o7-machinehum/flipper-blackhat-a33/electronics/nff_pcb/a33_power.kicad_sch

## KiCad design electronics/nff_pcb/a33_power.kicad_sch (2024-08-12)

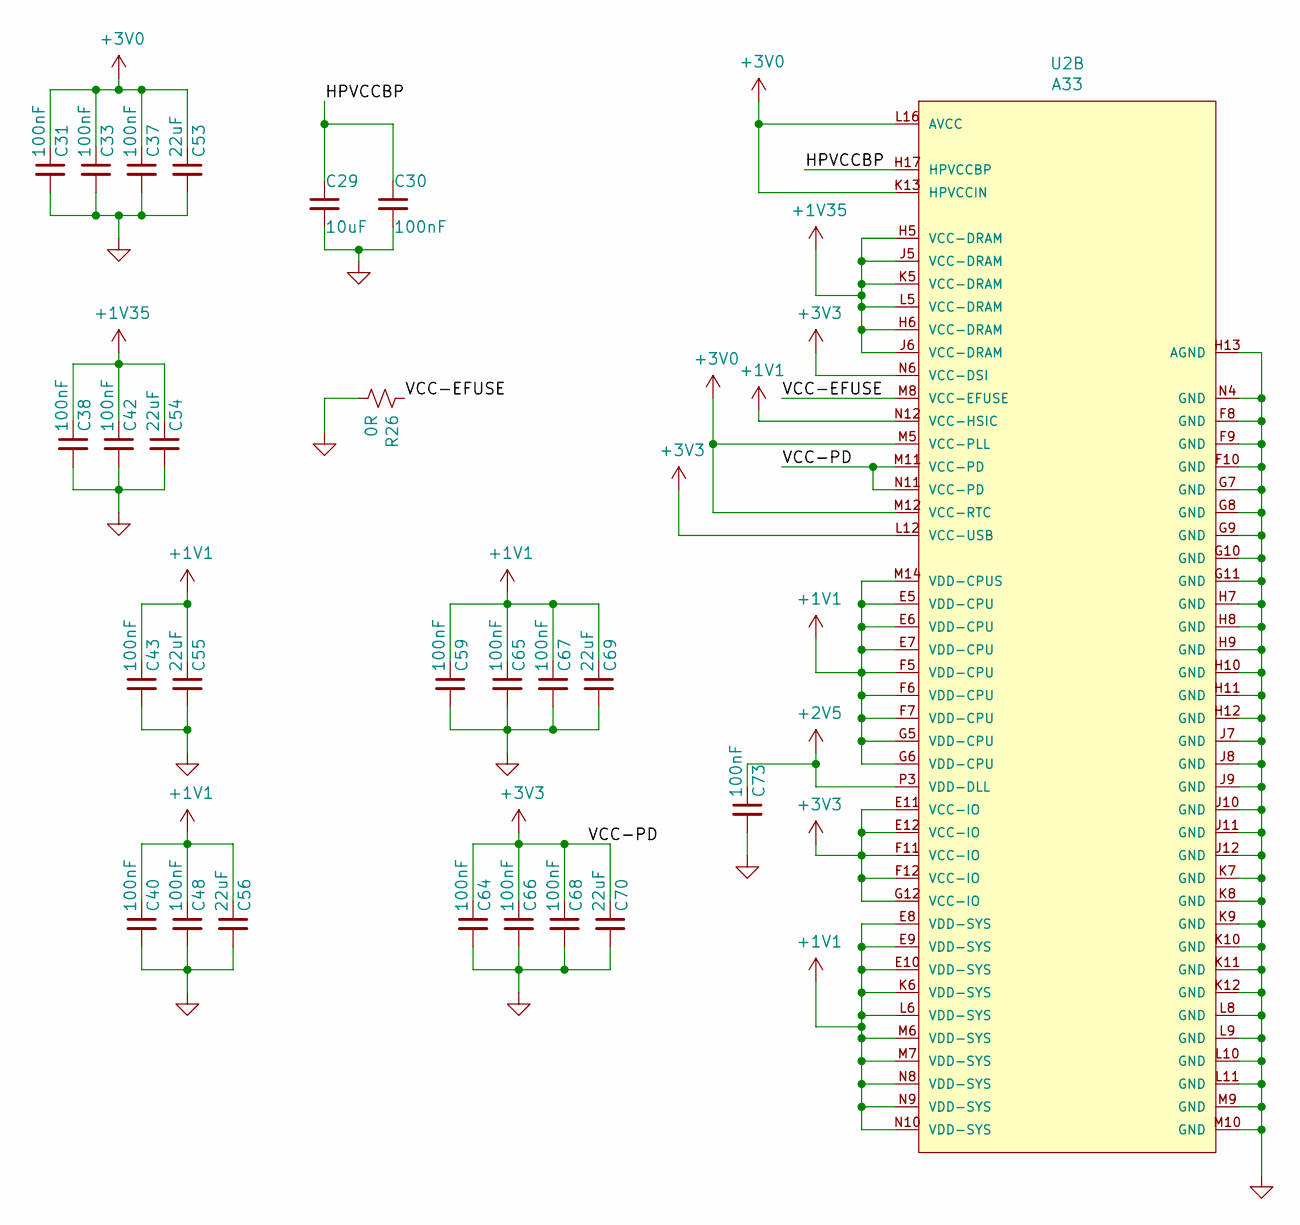
[picture p10: schematic a33_power.kicad_sch]

Parts:
C29: 10uF; C_0402_1005Metric; MPN CL05A106MQ5NUNC
C30, C31, C33, C37, C38, C40, C42, C43, C48, C59, C64, C65, C66, C67, C68, C73: 100nF; C_0402_1005Metric; MPN CC0402KRX7R7BB104
C53, C54, C55, C56, C69, C70: 22uF; C_0402_1005Metric; MPN GRM158R60J226ME01D
R26: 0R; R_0402_1005Metric; MPN RC0402JR-070RL
U2: A33; Allwinner_Technology_Co.,_Ltd.-A33-0; MPN "Allwinner A33" or "Allwinner R16"

Connections:
+1V1: C40.1, C43.1, C48.1, C55.1, C56.1, C59.1, C65.1, C67.1, C69.1, U2.E5 (VDD-CPU), U2.E6 (VDD-CPU), U2.E7 (VDD-CPU), U2.E8 (VDD-SYS), U2.E9 (VDD-SYS), U2.E10 (VDD-SYS), U2.F5 (VDD-CPU), U2.F6 (VDD-CPU), U2.F7 (VDD-CPU), U2.G5 (VDD-CPU), U2.G6 (VDD-CPU), U2.K6 (VDD-SYS), U2.L6 (VDD-SYS), U2.M6 (VDD-SYS), U2.M7 (VDD-SYS), U2.M14 (VDD-CPUS), U2.N8 (VDD-SYS), U2.N9 (VDD-SYS), U2.N10 (VDD-SYS), U2.N12 (VCC-HSIC)
+1V35: C38.1, C42.1, C54.1, U2.H5 (VCC-DRAM), U2.H6 (VCC-DRAM), U2.J5 (VCC-DRAM), U2.J6 (VCC-DRAM), U2.K5 (VCC-DRAM), U2.L5 (VCC-DRAM)
+2V5: C73.1, U2.P3 (VDD-DLL)
+3V0: C31.1, C33.1, C37.1, C53.1, U2.K13 (HPVCCIN), U2.L16 (AVCC), U2.M5 (VCC-PLL), U2.M12 (VCC-RTC)
+3V3: C64.1, C66.1, C68.1, C70.1, U2.E11 (VCC-IO), U2.E12 (VCC-IO), U2.F11 (VCC-IO), U2.F12 (VCC-IO), U2.G12 (VCC-IO), U2.L12 (VCC-USB), U2.M11 (VCC-PD), U2.N6 (VCC-DSI), U2.N11 (VCC-PD)
GND: C29.2, C30.2, C31.2, C33.2, C37.2, C38.2, C40.2, C42.2, C43.2, C48.2, C53.2, C54.2, C55.2, C56.2, C59.2, C64.2, C65.2, C66.2, C67.2, C68.2, C69.2, C70.2, C73.2, R26.2, U2.F8 (GND), U2.F9 (GND), U2.F10 (GND), U2.G7 (GND), U2.G8 (GND), U2.G9 (GND), U2.G10 (GND), U2.G11 (GND), U2.H7 (GND), U2.H8 (GND), U2.H9 (GND), U2.H10 (GND), U2.H11 (GND), U2.H12 (GND), U2.H13 (AGND), U2.J7 (GND), U2.J8 (GND), U2.J9 (GND), U2.J10 (GND), U2.J11 (GND), U2.J12 (GND), U2.K7 (GND), U2.K8 (GND), U2.K9 (GND), U2.K10 (GND), U2.K11 (GND), U2.K12 (GND), U2.L8 (GND), U2.L9 (GND), U2.L10 (GND), U2.L11 (GND), U2.M9 (GND), U2.M10 (GND), U2.N4 (GND)
HPVCCBP: C29.1, C30.1, U2.H17 (HPVCCBP)
VCC-EFUSE: R26.1, U2.M8 (VCC-EFUSE)
