o7-machinehum/flipper-blackhat-a33/electronics/nff_pcb/a33_ram.kicad_sch

## KiCad design electronics/nff_pcb/a33_ram.kicad_sch (2024-08-12)

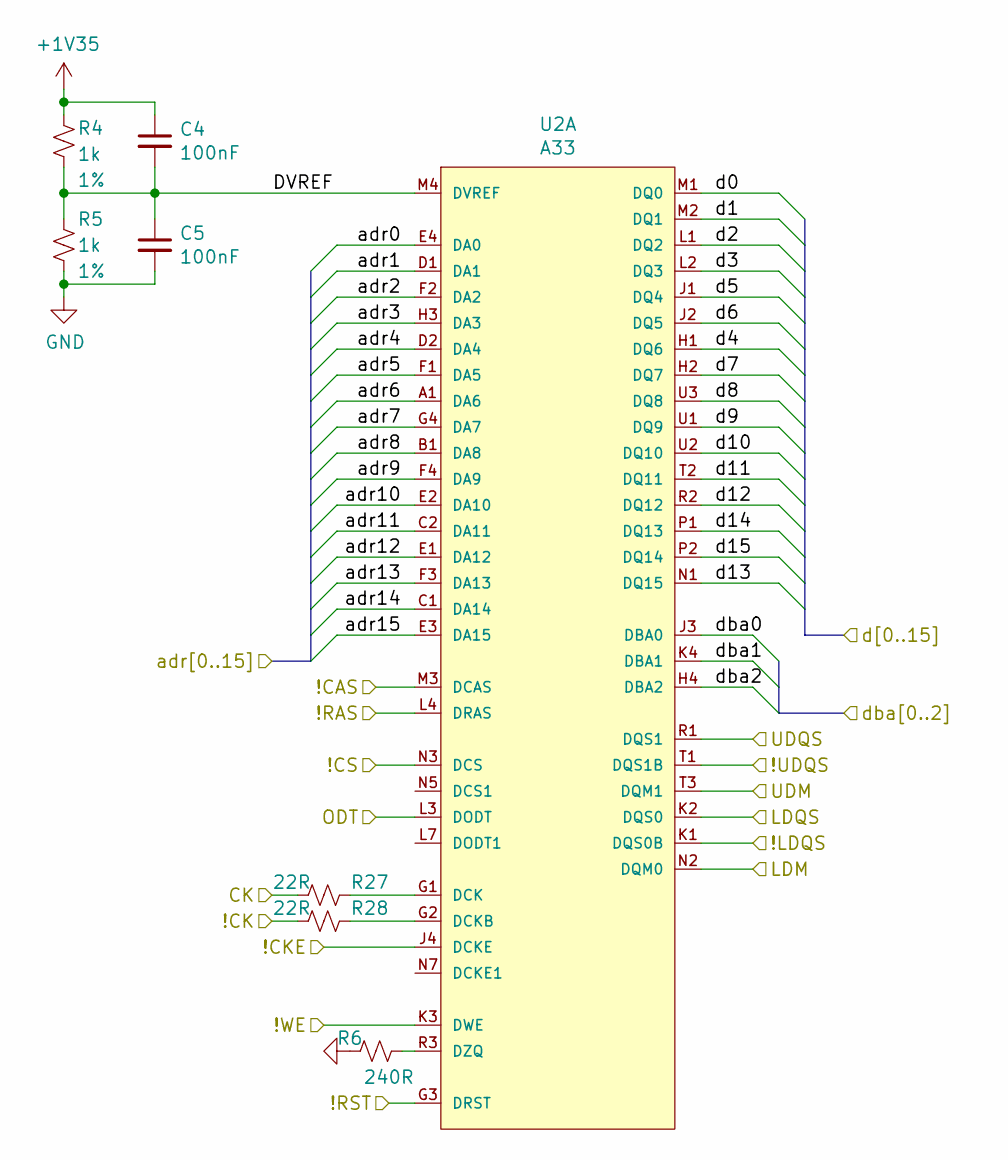
[picture p11: schematic a33_ram.kicad_sch]

Parts:
C4, C5: 100nF; C_0402_1005Metric; MPN CC0402KRX7R7BB104
R4, R5: 1k; R_0402_1005Metric; Tolerance 1%; MPN 4-1879208-9
R6: 240R; R_0402_1005Metric; MPN 0402WGF2400TCE
R27, R28: 22R; R_0402_1005Metric; MPN RC0402JR-0722RL
U2: A33; Allwinner_Technology_Co.,_Ltd.-A33-0; MPN "Allwinner A33" or "Allwinner R16"

Connections:
!CAS: U2.M3 (DCAS)
!CK: R28.2
!CKE: U2.J4 (DCKE)
!CS: U2.N3 (DCS)
!LDQS: U2.K1 (DQS0B)
!RAS: U2.L4 (DRAS)
!RST: U2.G3 (DRST)
!UDQS: U2.T1 (DQS1B)
!WE: U2.K3 (DWE)
+1V35: C4.1, R4.1
CK: R27.2
DVREF: C4.2, C5.1, R4.2, R5.1, U2.M4 (DVREF)
GND: C5.2, R5.2, R6.2
LDM: U2.N2 (DQM0)
LDQS: U2.K2 (DQS0)
unnamed: R6.1, U2.R3 (DZQ)
unnamed: R27.1, U2.G1 (DCK)
unnamed: R28.1, U2.G2 (DCKB)
ODT: U2.L3 (DODT)
UDM: U2.T3 (DQM1)
UDQS: U2.R1 (DQS1)
adr0: U2.E4 (DA0)
adr1: U2.D1 (DA1)
adr2: U2.F2 (DA2)
adr3: U2.H3 (DA3)
adr4: U2.D2 (DA4)
adr5: U2.F1 (DA5)
adr6: U2.A1 (DA6)
adr7: U2.G4 (DA7)
adr8: U2.B1 (DA8)
adr9: U2.F4 (DA9)
adr10: U2.E2 (DA10)
adr11: U2.C2 (DA11)
adr12: U2.E1 (DA12)
adr13: U2.F3 (DA13)
adr14: U2.C1 (DA14)
adr15: U2.E3 (DA15)
d0: U2.M1 (DQ0)
d1: U2.M2 (DQ1)
d2: U2.L1 (DQ2)
d3: U2.L2 (DQ3)
d4: U2.H1 (DQ6)
d5: U2.J1 (DQ4)
d6: U2.J2 (DQ5)
d7: U2.H2 (DQ7)
d8: U2.U3 (DQ8)
d9: U2.U1 (DQ9)
d10: U2.U2 (DQ10)
d11: U2.T2 (DQ11)
d12: U2.R2 (DQ12)
d13: U2.N1 (DQ15)
d14: U2.P1 (DQ13)
d15: U2.P2 (DQ14)
dba0: U2.J3 (DBA0)
dba1: U2.K4 (DBA1)
dba2: U2.H4 (DBA2)
