o7-machinehum/flipper-blackhat-a33/electronics/nff_pcb/dsi.kicad_sch

## KiCad design electronics/nff_pcb/dsi.kicad_sch (2024-08-12)

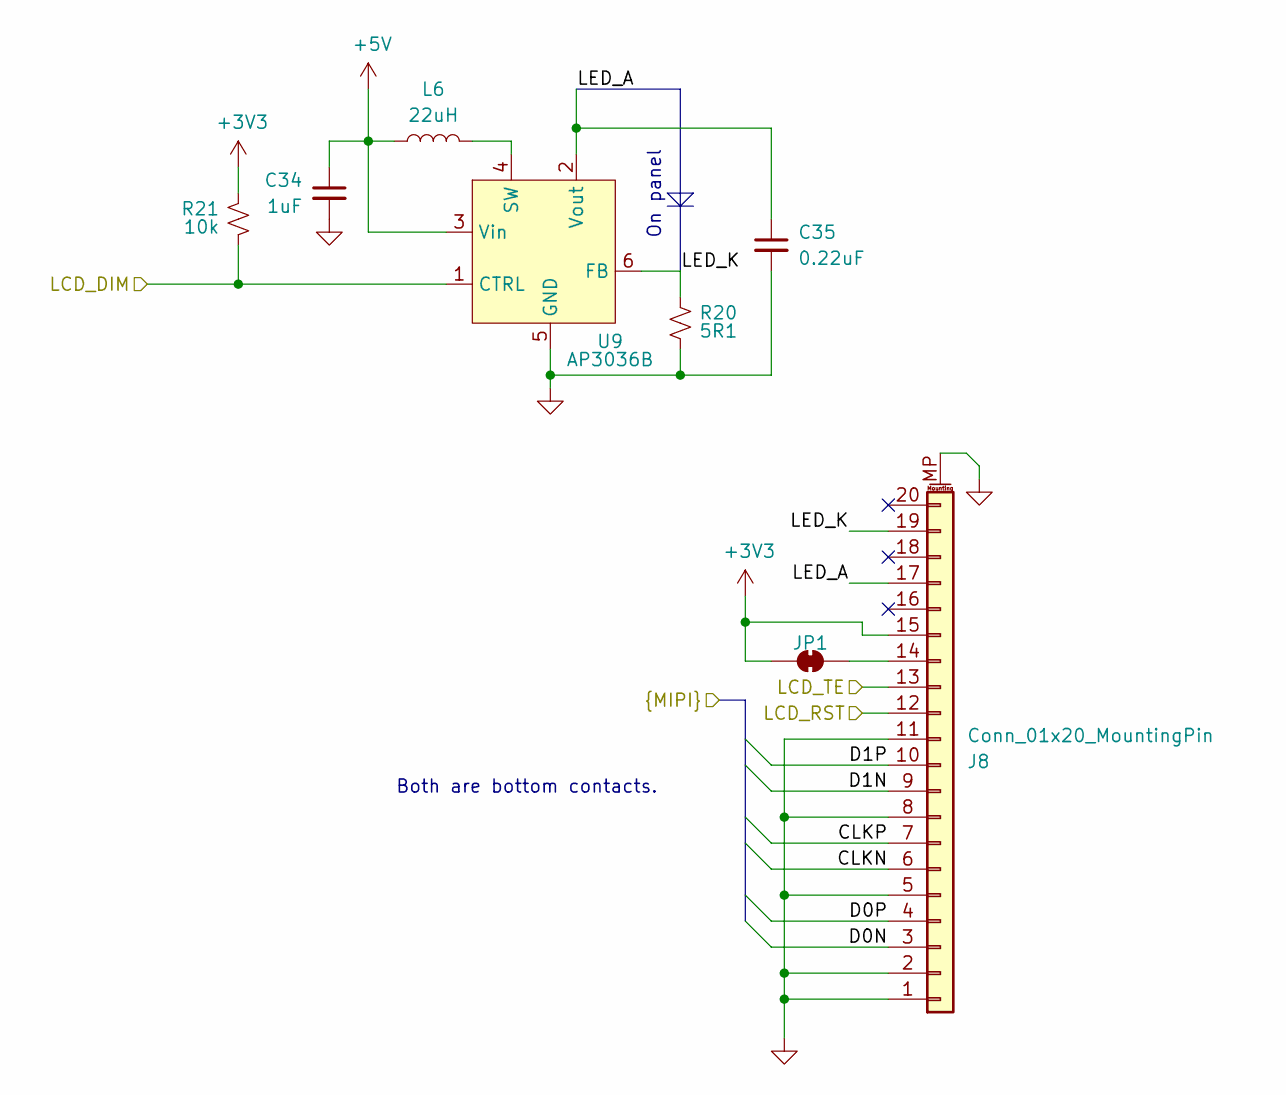
[picture p12: schematic dsi.kicad_sch]

Parts:
C34: 1uF; C_0402_1005Metric; MPN CL05A105KO5NNNC
C35: 0.22uF; C_0603_1608Metric; MPN CC0603KRX7R7BB224
J8: Conn_01x20_MountingPin; Hirose_FH12-20S-0.5SH_1x20-1MP_P0.50mm_Horizontal; MPN FH12-20S-0.5SH(55)
JP1: SolderJumper_2_Bridged; SolderJumper-2_P1.3mm_Bridged_Pad1.0x1.5mm
L6: 22uH; L_1210_3225Metric; MPN CBC3225T220MR
R20: 5R1; R_0402_1005Metric; MPN RC0402JR-075R1L
R21: 10k; R_0402_1005Metric; MPN RC0402JR-0710KL
U9: AP3036B; SOT-23-6; MPN AP3036BKTR-G1

Connections:
+3V3: J8.15, JP1.1 (A), R21.1
+5V: C34.1, L6.1, U9.3 (Vin)
CLKN: J8.6
CLKP: J8.7
D0N: J8.3
D0P: J8.4
D1N: J8.9
D1P: J8.10
GND: C34.2, C35.2, J8.1, J8.2, J8.5, J8.8, J8.11, J8.MP (MountPin), R20.2, U9.5 (GND)
LCD_DIM: R21.2, U9.1 (CTRL)
LCD_RST: J8.12
LCD_TE: J8.13
LED_A: C35.1, J8.17, U9.2 (Vout)
LED_K: J8.19, R20.1, U9.6 (FB)
unnamed: J8.14, JP1.2 (B)
unnamed: L6.2, U9.4 (SW)

Notes on the sheet:
Both are bottom contacts.
On panel
