o7-machinehum/flipper-blackhat-a33/electronics/nff_pcb/gpio.kicad_sch

## KiCad design electronics/nff_pcb/gpio.kicad_sch (2024-12-25)

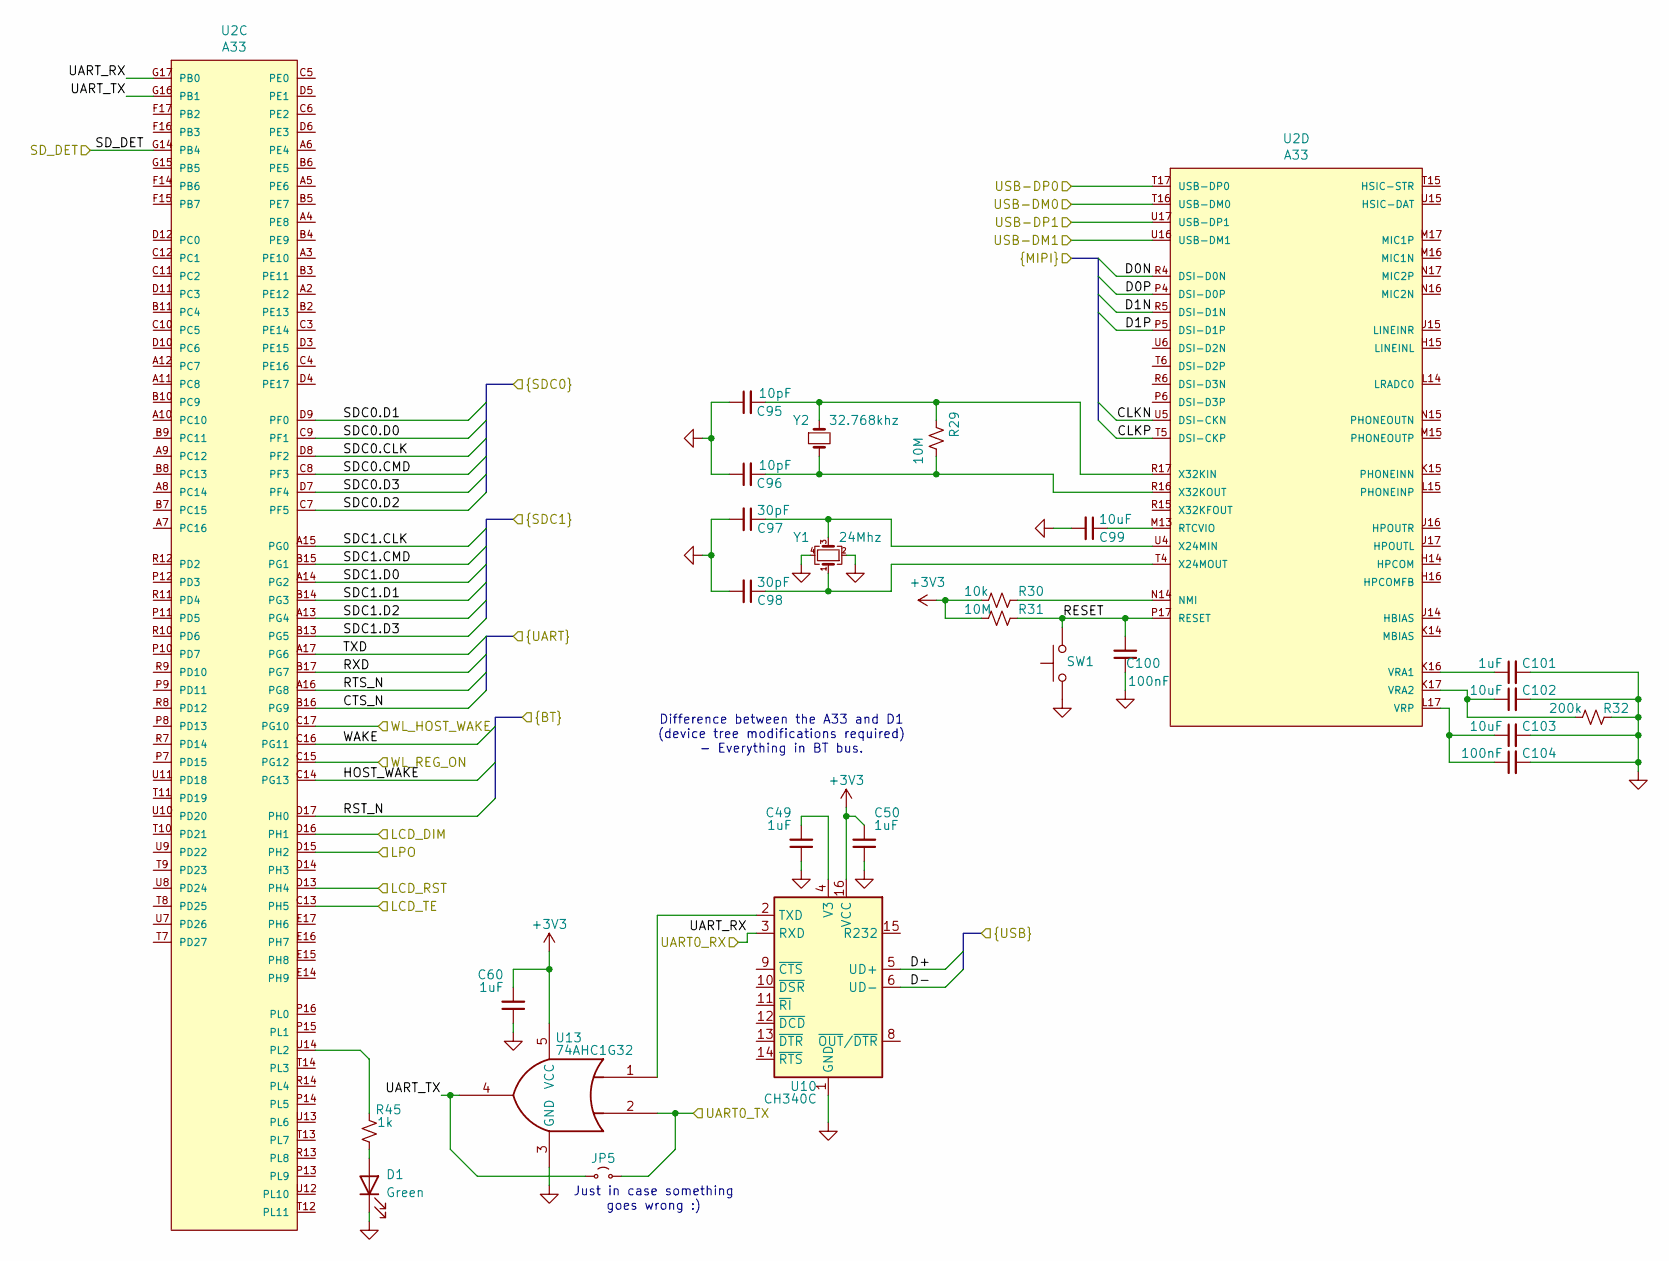
[picture p13: schematic gpio.kicad_sch]

Parts:
C49, C50, C60, C101: 1uF; C_0402_1005Metric; MPN CL05A105KO5NNNC
C95, C96: 10pF; C_0402_1005Metric; MPN CC0402JRNPO9BN100
C97, C98: 30pF; C_0402_1005Metric; MPN CC0402JRNPO9BN300
C99, C102, C103: 10uF; C_0402_1005Metric; MPN CL05A106MQ5NUNC
C100, C104: 100nF; C_0402_1005Metric; MPN CC0402KRX7R7BB104
D1: Green; LED_0603_1608Metric; MPN LTST-C193TGKT-5A
JP5: Jumper_2_Small_Open; SolderJumper-2_P1.3mm_Open_RoundedPad1.0x1.5mm
R29, R31: 10M; R_0402_1005Metric; MPN 0402WGJ0106TCE
R30: 10k; R_0402_1005Metric; MPN RC0402JR-0710KL
R32: 200k; R_0402_1005Metric; MPN RC0402FR-07200KL
R45: 1k; R_0402_1005Metric; MPN RC0402JR-071KL
SW1: SW_Push; SW_SPST_TL3305A; MPN TL3305AF260QG
U2: A33; Allwinner_Technology_Co.,_Ltd.-A33-0; MPN "Allwinner A33" or "Allwinner R16"
U10: CH340C; SOIC-16_3.9x9.9mm_P1.27mm; MPN CH340C
U13: 74AHC1G32; SOT-353_SC-70-5; MPN SN74LVC1G32DCKT
Y1: 24Mhz; Crystal_SMD_Abracon_ABM8G-4Pin_3.2x2.5mm; MPN ABM8G-24.000MHZ-18-D2Y-T
Y2: 32.768khz; Abracon-ABS05-0-0-MFG; MPN ABS05-32.768KHZ-9-T

Connections:
+3V3: C50.2, C60.2, R30.2, R31.2, U10.16 (VCC), U13.5 (VCC)
CLKN: U2.U5 (DSI-CKN)
CLKP: U2.T5 (DSI-CKP)
CTS_N: U2.B16 (PG9)
D0N: U2.R4 (DSI-D0N)
D0P: U2.P4 (DSI-D0P)
D1N: U2.R5 (DSI-D1N)
D1P: U2.P5 (DSI-D1P)
D+: U10.5 (UD+)
D-: U10.6 (UD-)
GND: C49.1, C50.1, C60.1, C95.1, C96.1, C97.2, C98.2, C99.2, C100.1, C101.2, C102.2, C103.2, C104.2, D1.1 (K), R32.1, SW1.1, U10.1 (GND), U13.3 (GND), Y1.2, Y1.4
HOST_WAKE: U2.C14 (PG13)
LCD_DIM: U2.D16 (PH1)
LCD_RST: U2.D13 (PH4)
LCD_TE: U2.C13 (PH5)
LPO: U2.D15 (PH2)
unnamed: C49.2, U10.4 (V3)
unnamed: C95.2, R29.1, U2.R17 (X32KIN), Y2.1
unnamed: C96.2, R29.2, U2.R16 (X32KOUT), Y2.2
unnamed: C97.1, U2.U4 (X24MIN), Y1.3
unnamed: C98.1, U2.T4 (X24MOUT), Y1.1
unnamed: C99.1, U2.M13 (RTCVIO)
unnamed: C101.1, U2.K16 (VRA1)
unnamed: C102.1, R32.2, U2.K17 (VRA2)
unnamed: C103.1, C104.1, U2.L17 (VRP)
unnamed: D1.2 (A), R45.2
unnamed: R30.1, U2.N14 (NMI)
unnamed: R45.1, U2.U14 (PL2)
unnamed: U10.2 (TXD), U13.1
RESET: C100.2, R31.1, SW1.2, U2.P17 (RESET)
RST_N: U2.D17 (PH0)
RTS_N: U2.A16 (PG8)
RXD: U2.B17 (PG7)
SDC0.CLK: U2.D8 (PF2)
SDC0.CMD: U2.C8 (PF3)
SDC0.D0: U2.C9 (PF1)
SDC0.D1: U2.D9 (PF0)
SDC0.D2: U2.C7 (PF5)
SDC0.D3: U2.D7 (PF4)
SDC1.CLK: U2.A15 (PG0)
SDC1.CMD: U2.B15 (PG1)
SDC1.D0: U2.A14 (PG2)
SDC1.D1: U2.B14 (PG3)
SDC1.D2: U2.A13 (PG4)
SDC1.D3: U2.B13 (PG5)
SD_DET: U2.G14 (PB4)
TXD: U2.A17 (PG6)
UART0_RX: U2.G17 (PB0), U10.3 (RXD)
UART0_TX: JP5.2 (B), U13.2
UART_TX: JP5.1 (A), U2.G16 (PB1), U13.4
USB-DM0: U2.T16 (USB-DM0)
USB-DM1: U2.U16 (USB-DM1)
USB-DP0: U2.T17 (USB-DP0)
USB-DP1: U2.U17 (USB-DP1)
WAKE: U2.C16 (PG11)
WL_HOST_WAKE: U2.C17 (PG10)
WL_REG_ON: U2.C15 (PG12)

Notes on the sheet:
Just in case something goes wrong :)
Difference between the A33 and D1 (device tree modifications required) - Everything in BT bus.
