o7-machinehum/flipper-blackhat-a33/electronics/nff_pcb/hardware.kicad_sch

## KiCad design electronics/nff_pcb/hardware.kicad_sch (2024-12-25)

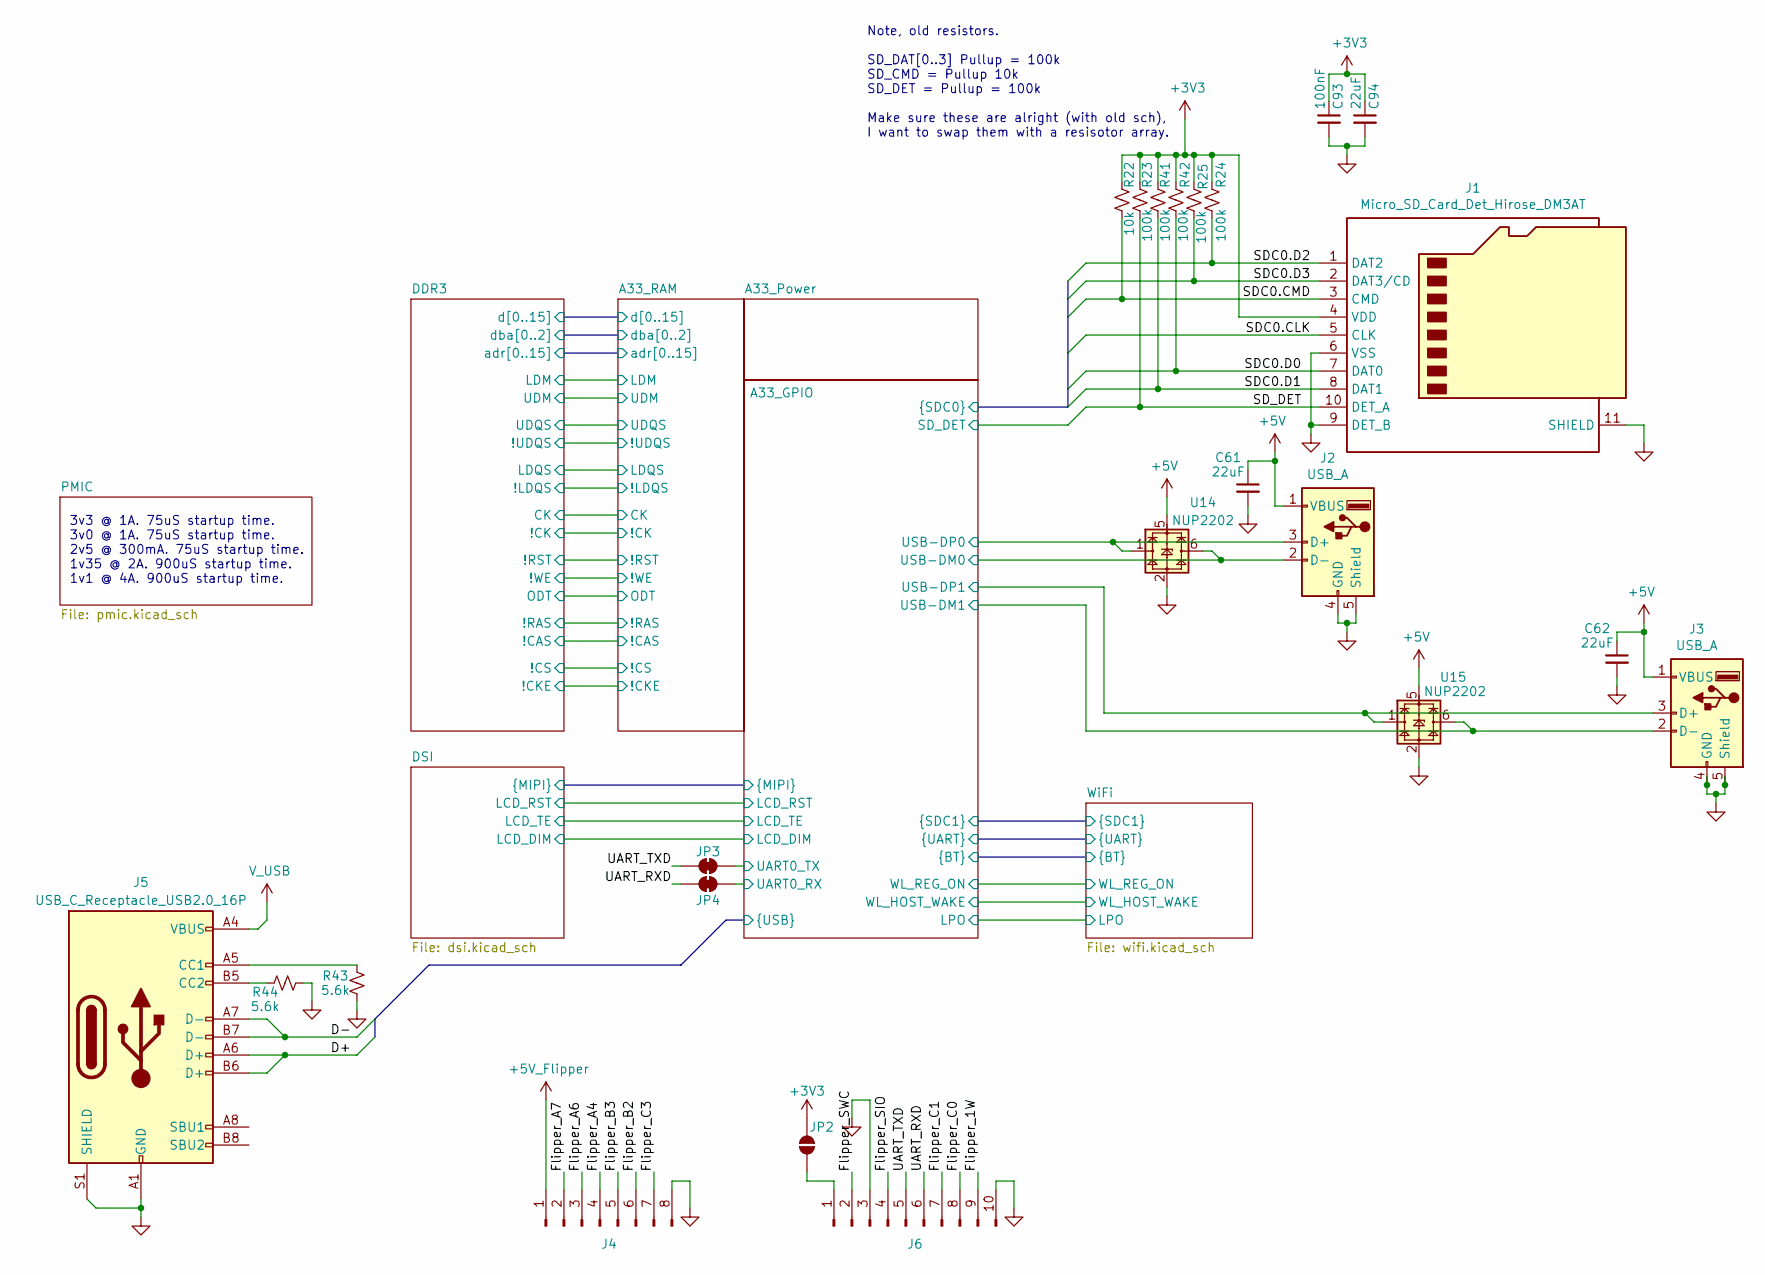
[picture p14: schematic hardware.kicad_sch]

Parts:
C61, C62, C94: 22uF; C_0402_1005Metric; MPN GRM158R60J226ME01D
C93: 100nF; C_0402_1005Metric; MPN CC0402KRX7R7BB104
J1: Micro_SD_Card_Det_Hirose_DM3AT; microSD_HC_Hirose_DM3AT-SF-PEJM5; MPN DM3AT-SF-PEJM5
J2, J3: USB_A; USB_A_Molex_105057_Vertical; MPN 1050570001
J4: Conn_01x08_Pin; PinHeader_1x08_P2.54mm_Horizontal; MPN PH1RB-08-UA
J5: USB_C_Receptacle_USB2.0_16P; USB_C_Receptacle_GCT_USB4105-xx-A_16P_TopMnt_Horizontal; MPN USB4105-GF-A-120
J6: Conn_01x10_Pin; PinHeader_1x10_P2.54mm_Horizontal; MPN PH1RB-10-UA
JP2: SolderJumper_2_Open; SolderJumper-2_P1.3mm_Open_RoundedPad1.0x1.5mm
JP3, JP4: SolderJumper_2_Bridged; SolderJumper-2_P1.3mm_Bridged_Pad1.0x1.5mm
R22: 10k; R_0402_1005Metric; MPN RC0402JR-0710KL
R23, R24, R25, R41, R42: 100k; R_0402_1005Metric; MPN RC0402FR-13100KL
R43, R44: 5.6k; R_0402_1005Metric; MPN RC0402FR-135K6L
U14, U15: NUP2202; SOT-363_SC-70-6; MPN NUP2202W1T2G

Connections:
+3V3: C93.1, C94.1, J1.4 (VDD), JP2.2 (B), R22.2, R23.2, R24.2, R25.2, R41.2, R42.2
+5V: C61.1, C62.1, J2.1 (VBUS), J3.1 (VBUS), U14.5, U15.5
+5V_Flipper: J4.1
D+: J5.A6 (D+), J5.B6 (D+)
D-: J5.A7 (D-), J5.B7 (D-)
Flipper_1W: J6.9
Flipper_A4: J4.4
Flipper_A6: J4.3
Flipper_A7: J4.2
Flipper_B2: J4.6
Flipper_B3: J4.5
Flipper_C0: J6.8
Flipper_C1: J6.7
Flipper_C3: J4.7
Flipper_SIO: J6.4
Flipper_SWC: J6.2
GND: C61.2, C62.2, C93.2, C94.2, J1.6 (VSS), J1.9 (DET_B), J1.11 (SHIELD), J2.4 (GND), J2.5 (Shield), J3.4 (GND), J3.5 (Shield), J4.8, J5.A1 (GND), J5.A12 (GND), J5.B1 (GND), J5.B12 (GND), J5.S1 (SHIELD), J6.3, J6.10, R43.1, R44.1, U14.2, U15.2
unnamed: J5.A5 (CC1), R43.2
unnamed: J5.B5 (CC2), R44.2
unnamed: J6.1, JP2.1 (A)
SDC0.CLK: J1.5 (CLK)
SDC0.CMD: J1.3 (CMD), R22.1
SDC0.D0: J1.7 (DAT0), R42.1
SDC0.D1: J1.8 (DAT1), R41.1
SDC0.D2: J1.1 (DAT2), R24.1
SDC0.D3: J1.2 (DAT3/CD), R25.1
SD_DET: J1.10 (DET_A), R23.1
UART0_RX: JP4.1 (A)
UART0_TX: JP3.1 (A)
UART_RXD: J6.6, JP4.2 (B)
UART_TXD: J6.5, JP3.2 (B)
USB-DM0: J2.2 (D-), U14.6
USB-DM1: J3.2 (D-), U15.6
USB-DP0: J2.3 (D+), U14.1
USB-DP1: J3.3 (D+), U15.1
V_USB: J5.A4 (VBUS), J5.A9 (VBUS), J5.B4 (VBUS), J5.B9 (VBUS)

Notes on the sheet:
Note, old resistors. SD_DAT[0..3] Pullup = 100k SD_CMD = Pullup 10k SD_DET = Pullup = 100k Make sure these are alright (with old sch), I want to swap them with a resisotor array.
3v3 @ 1A. 75uS startup time. 3v0 @ 1A. 75uS startup time. 2v5 @ 300mA. 75uS startup time. 1v35 @ 2A. 900uS startup time. 1v1 @ 4A. 900uS startup time.
