o7-machinehum/flipper-blackhat-a33/electronics/nff_pcb/pmic.kicad_sch

## KiCad design electronics/nff_pcb/pmic.kicad_sch (2024-12-25)

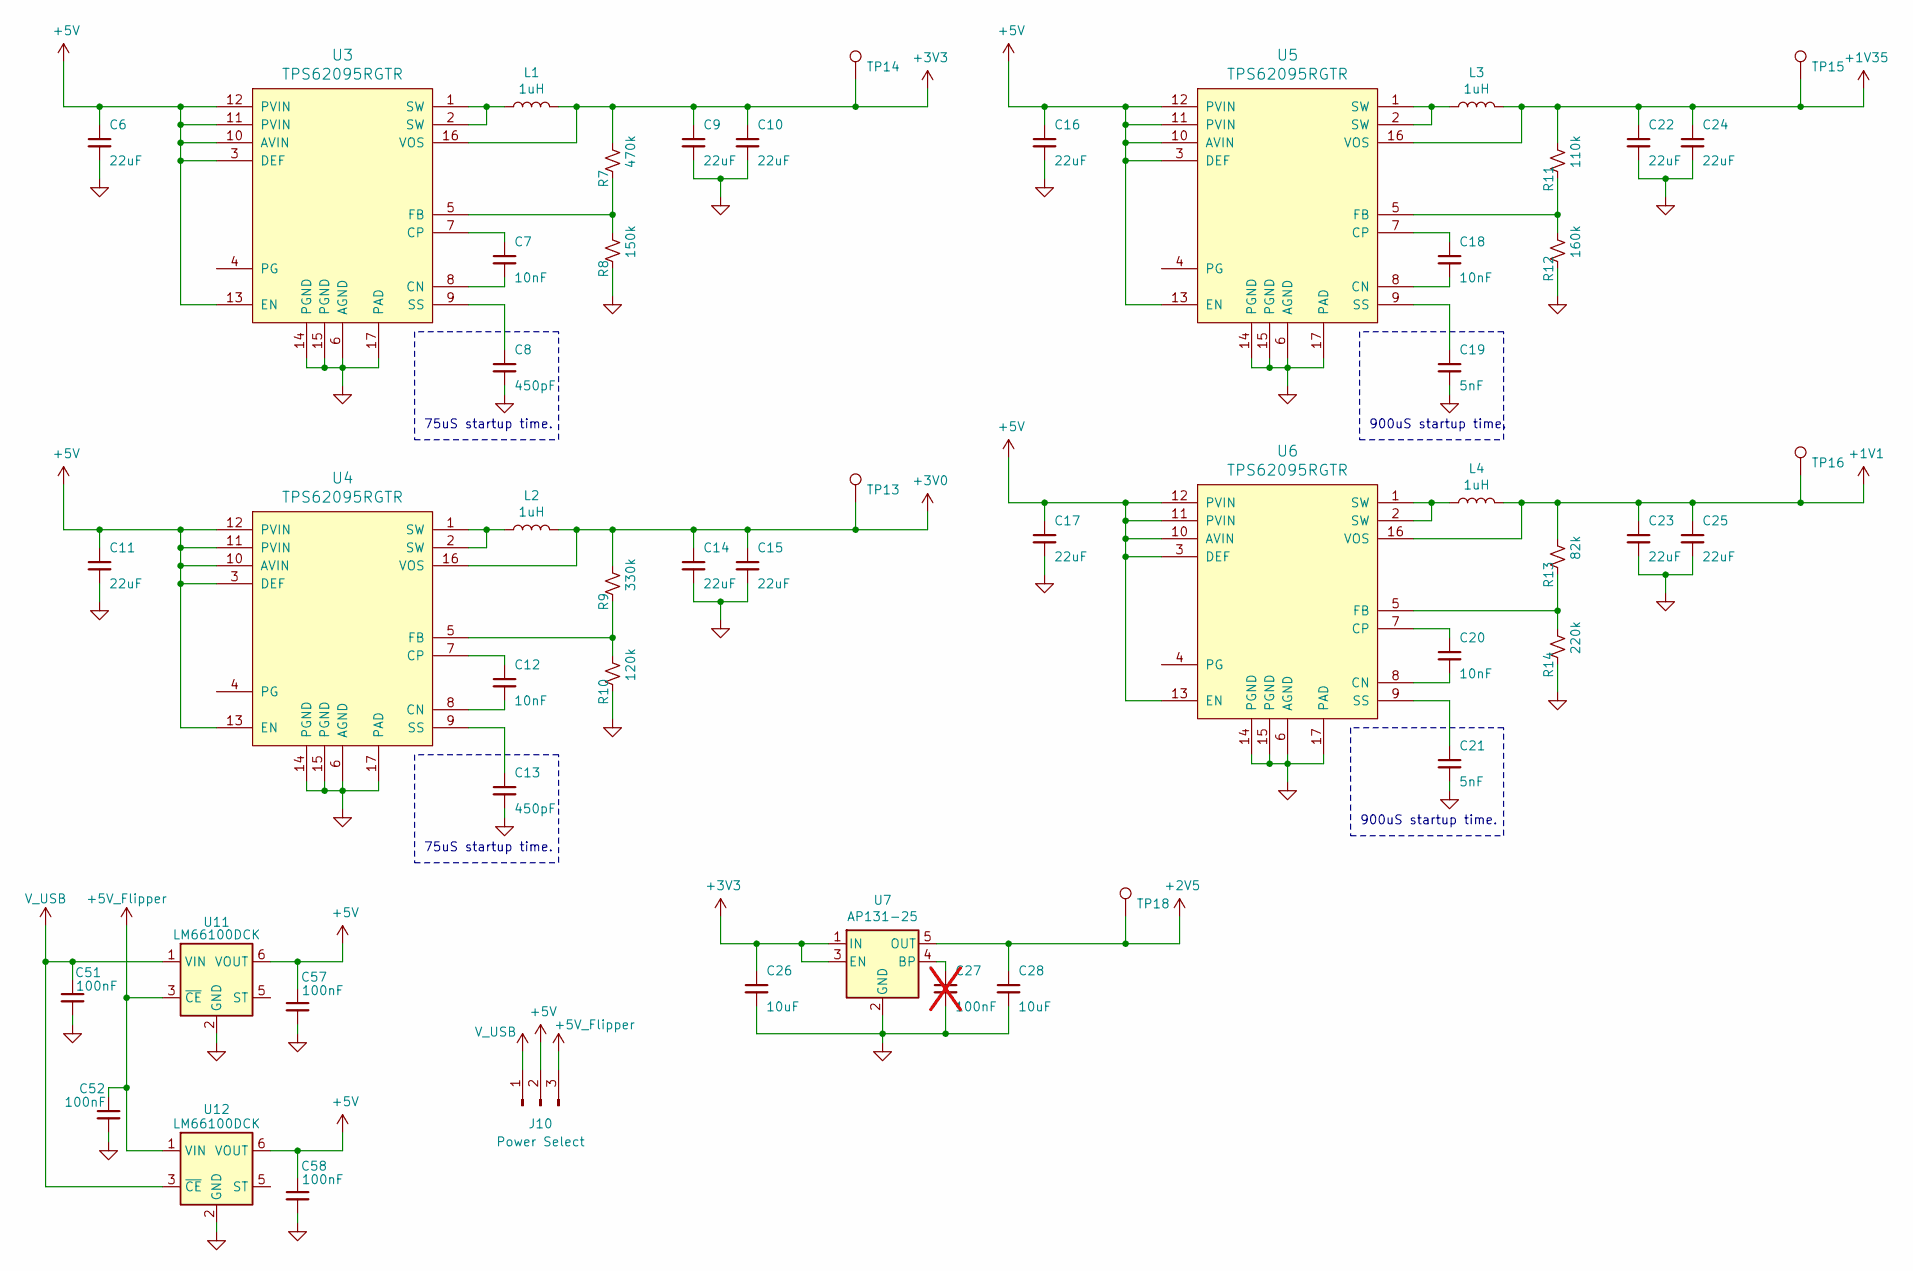
[picture p15: schematic pmic.kicad_sch]

Parts:
C6, C9, C10, C11, C14, C15, C16, C17, C22, C23, C24, C25: 22uF; C_0805_2012Metric; MPN CL21A226MQQNNNE
C7, C12, C18, C20: 10nF; C_0402_1005Metric; MPN CL05B103KB5NNNC
C8, C13: 450pF; C_0402_1005Metric; MPN CL05B471KB5NNNC
C19, C21: 5nF; C_0402_1005Metric; MPN CC0402KRX7R9BB562
C26, C28: 10uF; C_0805_2012Metric; MPN GRM21BR70J106KE76L
C27: 100nF; C_0402_1005Metric; MPN CC0402KRX7R7BB104; not fitted
C51, C52, C57, C58: 100nF; C_0402_1005Metric; MPN CC0402KRX7R7BB104
J10: Power Select; PinHeader_1x03_P2.54mm_Vertical
L1, L2, L3, L4: 1uH; SNH.4020.TYB1R0MT00; MPN SNH.4020.TYB1R0MT00
R7: 470k; R_0402_1005Metric; MPN RTT024703FTH
R8: 150k; R_0402_1005Metric; MPN RC0402FR-07150KL
R9: 330k; R_0402_1005Metric; MPN RC0402FR-07330KL
R10: 120k; R_0402_1005Metric; MPN RTT021203FTH
R11: 110k; R_0402_1005Metric; MPN RTT021103FTH
R12: 160k; R_0402_1005Metric; MPN 0402WGF1603TCE
R13: 82k; R_0402_1005Metric; MPN 0402WGF8202TCE
R14: 220k; R_0402_1005Metric; MPN ERJPA2F2203X
TP13, TP14, TP15, TP16, TP18: TestPoint; TestPoint_Pad_1.0x1.0mm
U3, U4, U5, U6: TPS62095RGTR; TI_RTE_S-PWQFN-N16; MPN TPS62095RGTR
U7: AP131-25; SOT-23-5; MPN AP7331-25WG-7
U11, U12: LM66100DCK; SOT-363_SC-70-6; MPN LM66100DCKR

Connections:
+1V1: C23.1, C25.1, L4.2, R13.1, TP16.1, U6.16 (VOS)
+1V35: C22.1, C24.1, L3.2, R11.1, TP15.1, U5.16 (VOS)
+2V5: C28.1, TP18.1, U7.5 (OUT)
+3V0: C14.1, C15.1, L2.2, R9.1, TP13.1, U4.16 (VOS)
+3V3: C9.1, C10.1, C26.1, L1.2, R7.1, TP14.1, U3.16 (VOS), U7.1 (IN), U7.3 (EN)
+5V: C6.1, C11.1, C16.1, C17.1, C57.1, C58.1, J10.2, U3.3 (DEF), U3.10 (AVIN), U3.11 (PVIN), U3.12 (PVIN), U3.13 (EN), U4.3 (DEF), U4.10 (AVIN), U4.11 (PVIN), U4.12 (PVIN), U4.13 (EN), U5.3 (DEF), U5.10 (AVIN), U5.11 (PVIN), U5.12 (PVIN), U5.13 (EN), U6.3 (DEF), U6.10 (AVIN), U6.11 (PVIN), U6.12 (PVIN), U6.13 (EN), U11.6 (VOUT), U12.6 (VOUT)
+5V_Flipper: C52.1, J10.3, U11.3 (~CE), U12.1 (VIN)
GND: C6.2, C8.2, C9.2, C10.2, C11.2, C13.2, C14.2, C15.2, C16.2, C17.2, C19.2, C21.2, C22.2, C23.2, C24.2, C25.2, C26.2, C27.2, C28.2, C51.2, C52.2, C57.2, C58.2, R8.2, R10.2, R12.2, R14.2, U3.6 (AGND), U3.14 (PGND), U3.15 (PGND), U3.17 (PAD), U4.6 (AGND), U4.14 (PGND), U4.15 (PGND), U4.17 (PAD), U5.6 (AGND), U5.14 (PGND), U5.15 (PGND), U5.17 (PAD), U6.6 (AGND), U6.14 (PGND), U6.15 (PGND), U6.17 (PAD), U7.2 (GND), U11.2 (GND), U12.2 (GND)
unnamed: C7.1, U3.7 (CP)
unnamed: C7.2, U3.8 (CN)
unnamed: C8.1, U3.9 (SS)
unnamed: C12.1, U4.7 (CP)
unnamed: C12.2, U4.8 (CN)
unnamed: C13.1, U4.9 (SS)
unnamed: C18.1, U5.7 (CP)
unnamed: C18.2, U5.8 (CN)
unnamed: C19.1, U5.9 (SS)
unnamed: C20.1, U6.7 (CP)
unnamed: C20.2, U6.8 (CN)
unnamed: C21.1, U6.9 (SS)
unnamed: C27.1, U7.4 (BP)
unnamed: L1.1, U3.1 (SW), U3.2 (SW)
unnamed: L2.1, U4.1 (SW), U4.2 (SW)
unnamed: L3.1, U5.1 (SW), U5.2 (SW)
unnamed: L4.1, U6.1 (SW), U6.2 (SW)
unnamed: R7.2, R8.1, U3.5 (FB)
unnamed: R9.2, R10.1, U4.5 (FB)
unnamed: R11.2, R12.1, U5.5 (FB)
unnamed: R13.2, R14.1, U6.5 (FB)
V_USB: C51.1, J10.1, U11.1 (VIN), U12.3 (~CE)

Notes on the sheet:
900uS startup time.
75uS startup time.
