o7-machinehum/flipper-blackhat-a33/electronics/nff_pcb/ram.kicad_sch

## KiCad design electronics/nff_pcb/ram.kicad_sch (2024-12-25)

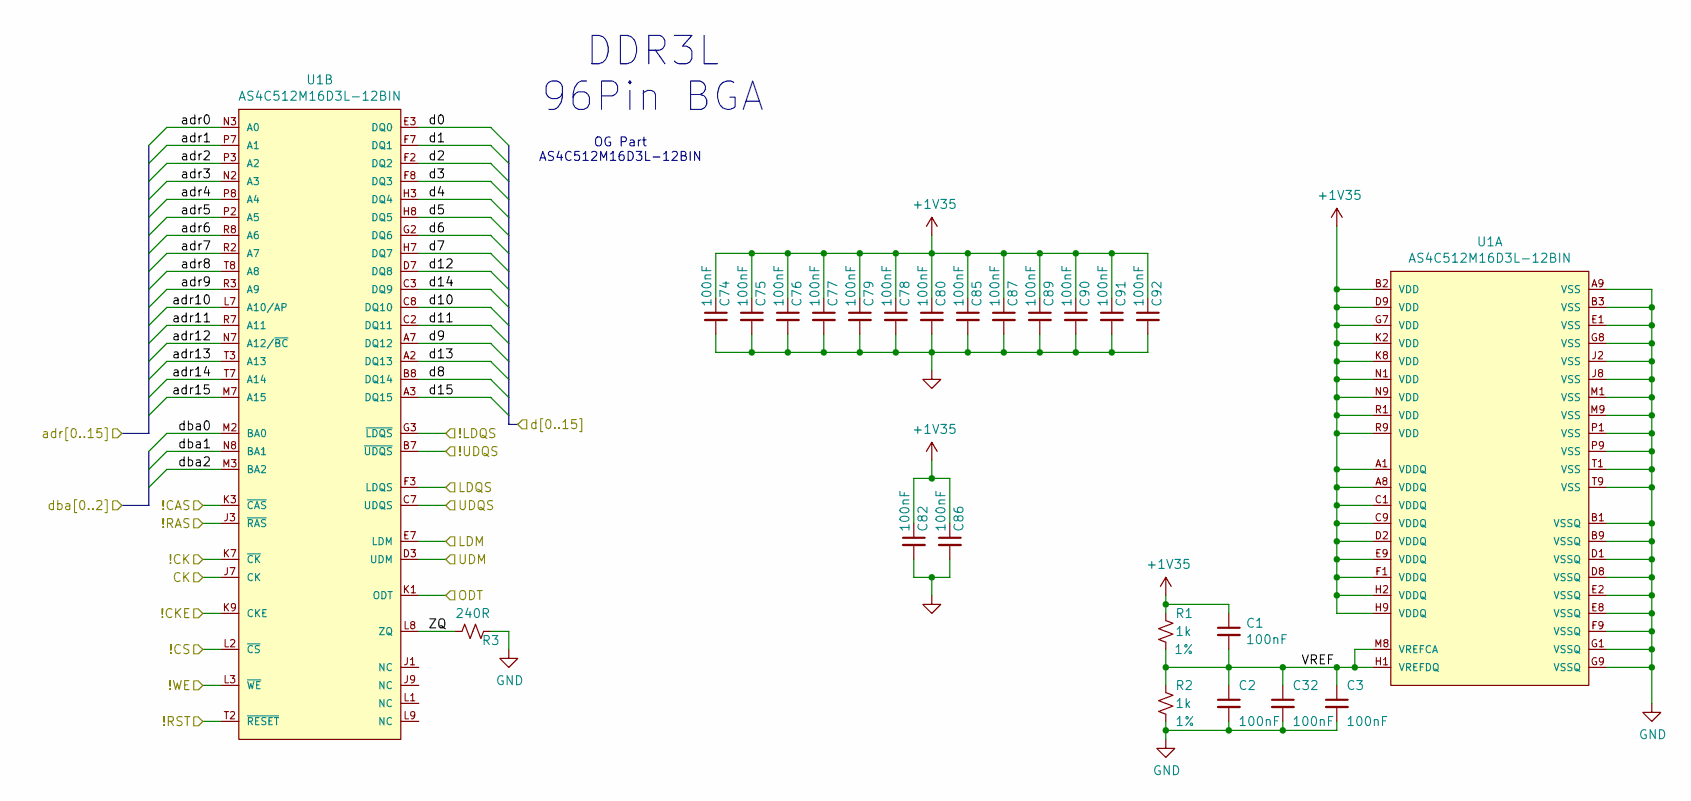
[picture p16: schematic ram.kicad_sch]

Parts:
C1, C2, C3, C32, C74, C75, C76, C77, C78, C79, C80, C82, C85, C86, C87, C89, C90, C91, C92: 100nF; C_0402_1005Metric; MPN CC0402KRX7R7BB104
R1, R2: 1k; R_0402_1005Metric; Tolerance 1%; MPN 4-1879208-9
R3: 240R; R_0402_1005Metric; MPN 0402WGF2400TCE
U1: AS4C512M16D3L-12BIN; Alliance_Memory-AS4C512M16D3L-12BIN-0-0-IPC_A; MPN ZDV4256M16A-13DPH

Connections:
!CAS: U1.K3 (~CAS)
!CK: U1.K7 (~CK)
!CKE: U1.K9 (CKE)
!CS: U1.L2 (~CS)
!LDQS: U1.G3 (~LDQS)
!RAS: U1.J3 (~RAS)
!RST: U1.T2 (~RESET)
!UDQS: U1.B7 (~UDQS)
!WE: U1.L3 (~WE)
+1V35: C1.1, C74.1, C75.1, C76.1, C77.1, C78.1, C79.1, C80.1, C82.1, C85.1, C86.1, C87.1, C89.1, C90.1, C91.1, C92.1, R1.1, U1.A1 (VDDQ), U1.A8 (VDDQ), U1.B2 (VDD), U1.C1 (VDDQ), U1.C9 (VDDQ), U1.D2 (VDDQ), U1.D9 (VDD), U1.E9 (VDDQ), U1.F1 (VDDQ), U1.G7 (VDD), U1.H2 (VDDQ), U1.H9 (VDDQ), U1.K2 (VDD), U1.K8 (VDD), U1.N1 (VDD), U1.N9 (VDD), U1.R1 (VDD), U1.R9 (VDD)
CK: U1.J7 (CK)
GND: C2.2, C3.2, C32.2, C74.2, C75.2, C76.2, C77.2, C78.2, C79.2, C80.2, C82.2, C85.2, C86.2, C87.2, C89.2, C90.2, C91.2, C92.2, R2.2, R3.1, U1.A9 (VSS), U1.B1 (VSSQ), U1.B3 (VSS), U1.B9 (VSSQ), U1.D1 (VSSQ), U1.D8 (VSSQ), U1.E1 (VSS), U1.E2 (VSSQ), U1.E8 (VSSQ), U1.F9 (VSSQ), U1.G1 (VSSQ), U1.G8 (VSS), U1.G9 (VSSQ), U1.J2 (VSS), U1.J8 (VSS), U1.M1 (VSS), U1.M9 (VSS), U1.P1 (VSS), U1.P9 (VSS), U1.T1 (VSS), U1.T9 (VSS)
LDM: U1.E7 (LDM)
LDQS: U1.F3 (LDQS)
ODT: U1.K1 (ODT)
UDM: U1.D3 (UDM)
UDQS: U1.C7 (UDQS)
VREF: C1.2, C2.1, C3.1, C32.1, R1.2, R2.1, U1.H1 (VREFDQ), U1.M8 (VREFCA)
ZQ: R3.2, U1.L8 (ZQ)
adr0: U1.N3 (A0)
adr1: U1.P7 (A1)
adr2: U1.P3 (A2)
adr3: U1.N2 (A3)
adr4: U1.P8 (A4)
adr5: U1.P2 (A5)
adr6: U1.R8 (A6)
adr7: U1.R2 (A7)
adr8: U1.T8 (A8)
adr9: U1.R3 (A9)
adr10: U1.L7 (A10/AP)
adr11: U1.R7 (A11)
adr12: U1.N7 (A12/~BC)
adr13: U1.T3 (A13)
adr14: U1.T7 (A14)
adr15: U1.M7 (A15)
d0: U1.E3 (DQ0)
d1: U1.F7 (DQ1)
d2: U1.F2 (DQ2)
d3: U1.F8 (DQ3)
d4: U1.H3 (DQ4)
d5: U1.H8 (DQ5)
d6: U1.G2 (DQ6)
d7: U1.H7 (DQ7)
d8: U1.B8 (DQ14)
d9: U1.A7 (DQ12)
d10: U1.C8 (DQ10)
d11: U1.C2 (DQ11)
d12: U1.D7 (DQ8)
d13: U1.A2 (DQ13)
d14: U1.C3 (DQ9)
d15: U1.A3 (DQ15)
dba0: U1.M2 (BA0)
dba1: U1.N8 (BA1)
dba2: U1.M3 (BA2)

Notes on the sheet:
OG Part AS4C512M16D3L-12BIN
DDR3L 96Pin BGA
