o7-machinehum/flipper-blackhat-a33/electronics/nff_pcb/wifi.kicad_sch

## KiCad design electronics/nff_pcb/wifi.kicad_sch (2024-12-25)

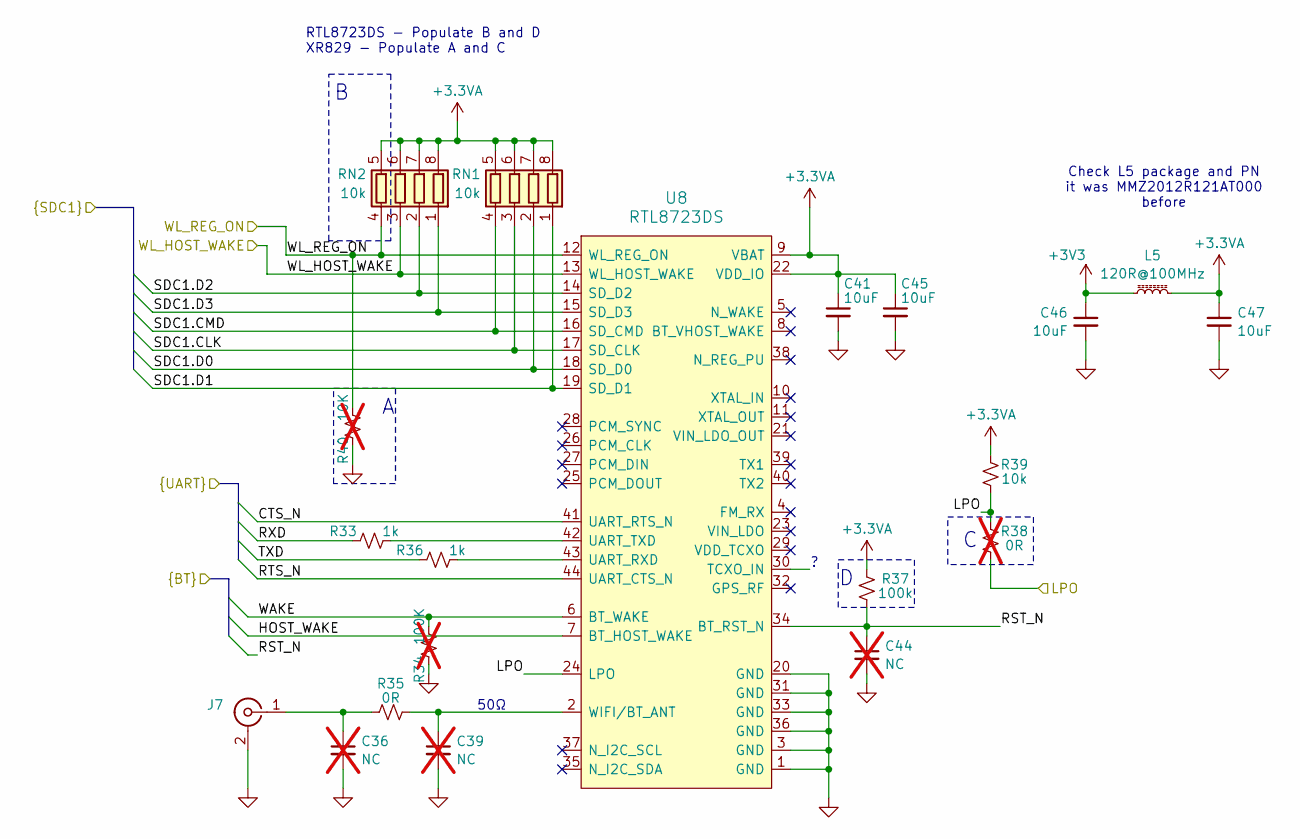
[picture p17: schematic wifi.kicad_sch]

Parts:
C36, C39, C44: NC; C_0402_1005Metric; not fitted
C41, C45, C46, C47: 10uF; C_0603_1608Metric; MPN LMK107BBJ106MALT
J7: Conn_Coaxial; SMA_Amphenol_901-143_Horizontal; MPN SMA-KWE901
L5: 120R@100MHz; L_0603_1608Metric; MPN BLM18KG121TN1D
R33, R36: 1k; R_0402_1005Metric; MPN RC0402JR-071KL
R34: 100K; R_0402_1005Metric; not fitted
R35: 0R; R_0402_1005Metric; MPN RC0402FR-070RL
R37: 100k; R_0402_1005Metric; MPN RC0402FR-13100KL
R38: 0R; R_0402_1005Metric; not fitted
R39: 10k; R_0402_1005Metric; MPN RC0402JR-0710KL
R40: 10K; R_0402_1005Metric; not fitted
RN1, RN2: 10k; R_Array_Convex_4x0402; MPN 4D02WGJ0103TCE
U8: RTL8723DS; RTL8723; MPN RTL8723DS

Connections:
+3.3VA: C41.1, C45.1, C47.1, L5.2, R37.2, R39.2, RN1.5 (R4.2), RN1.6 (R3.2), RN1.7 (R2.2), RN1.8 (R1.2), RN2.5 (R4.2), RN2.6 (R3.2), RN2.7 (R2.2), RN2.8 (R1.2), U8.9 (VBAT), U8.22 (VDD_IO)
+3V3: C46.1, L5.1
CTS_N: U8.41 (UART_RTS_N)
GND: C36.2, C39.2, C41.2, C44.2, C45.2, C46.2, C47.2, J7.2 (Ext), R34.1, R40.1, U8.1 (GND), U8.3 (GND), U8.20 (GND), U8.31 (GND), U8.33 (GND), U8.36 (GND)
HOST_WAKE: U8.7 (BT_HOST_WAKE)
LPO: R38.1, R38.2, R39.1, U8.24 (LPO)
unnamed: C36.1, J7.1 (In), R35.1
unnamed: C39.1, R35.2, U8.2 (WIFI/BT_ANT)
unnamed: R33.2, U8.42 (UART_TXD)
unnamed: R36.2, U8.43 (UART_RXD)
RST_N: C44.1, R37.1, U8.34 (BT_RST_N)
RTS_N: U8.44 (UART_CTS_N)
RXD: R33.1
SDC1.CLK: RN1.3 (R3.1), U8.17 (SD_CLK)
SDC1.CMD: RN1.4 (R4.1), U8.16 (SD_CMD)
SDC1.D0: RN1.2 (R2.1), U8.18 (SD_D0)
SDC1.D1: RN1.1 (R1.1), U8.19 (SD_D1)
SDC1.D2: RN2.2 (R2.1), U8.14 (SD_D2)
SDC1.D3: RN2.1 (R1.1), U8.15 (SD_D3)
TXD: R36.1
WAKE: R34.2, U8.6 (BT_WAKE)
WL_HOST_WAKE: RN2.3 (R3.1), U8.13 (WL_HOST_WAKE)
WL_REG_ON: R40.2, RN2.4 (R4.1), U8.12 (WL_REG_ON)

Notes on the sheet:
Check L5 package and PN it was MMZ2012R121AT000 before
RTL8723DS - Populate B and D XR829 - Populate A and C
50Ω
